ANDREW-Li-33/john-stockbot-3651/CAD files/flywheel printed parts/motor side inner bracket.stl

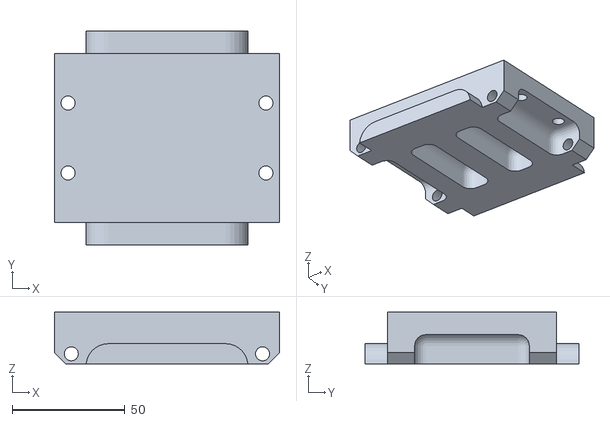
[picture p35: CAD file, 2026-05-08]
CAD files/flywheel printed parts/motor side inner bracket.stl
100.0 x 95.0 x 23.0
