ANDREW-Li-33/john-stockbot-3651/CAD files/drivetrain printed parts/wheel_90T_pulley.stl

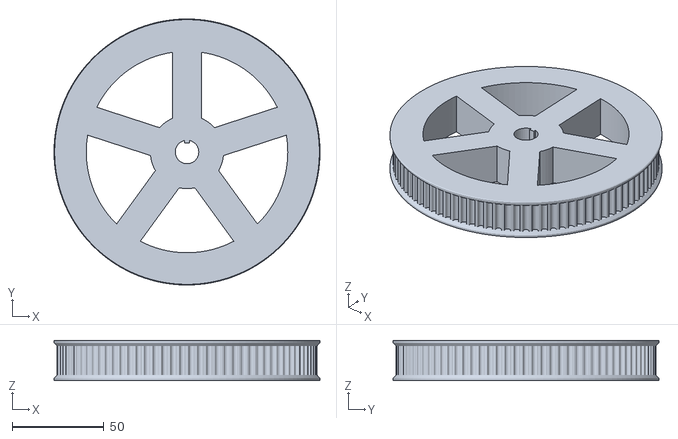
[picture p36: CAD file, 2026-05-08]
CAD files/drivetrain printed parts/wheel_90T_pulley.stl
145.2 x 145.2 x 22.0
