ANDREW-Li-33/john-stockbot-3651/CAD files/final project 3651/lighter_converyor_wheel.stl

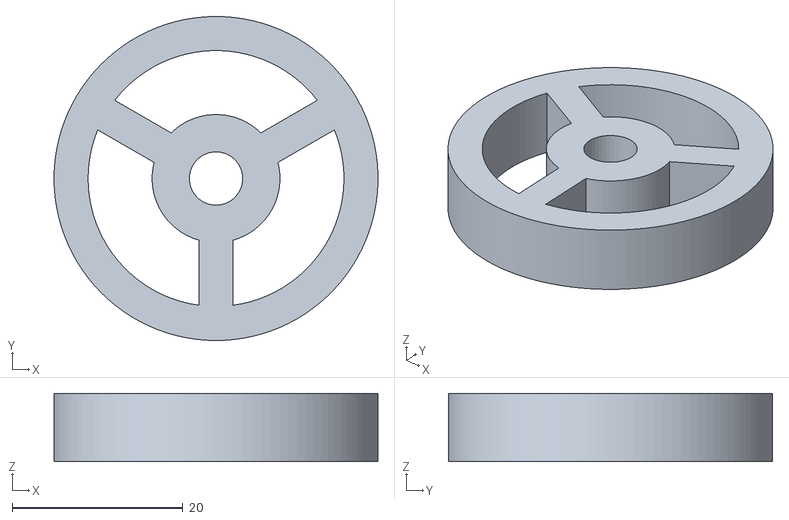
[picture p37: CAD file, 2026-05-08]
CAD files/final project 3651/lighter_converyor_wheel.stl
38.0 x 38.0 x 8.00
