ANDREW-Li-33/john-stockbot-3651/CAD files/drivetrain printed parts/4mm_high_spacer.stl

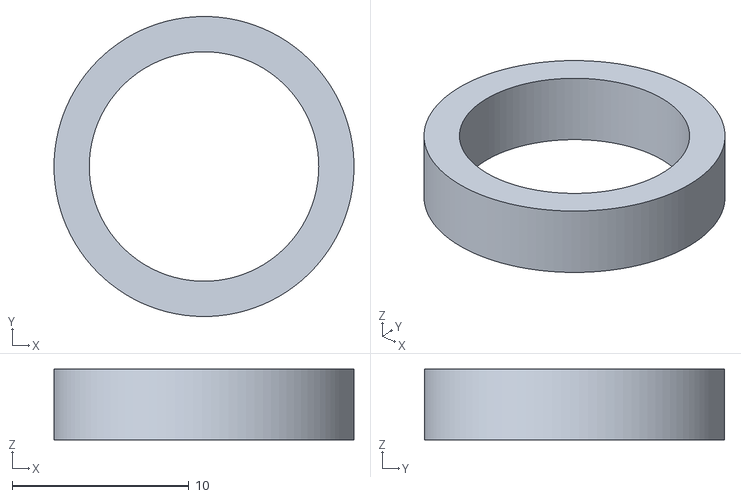
[picture p38: CAD file, 2026-05-08]
CAD files/drivetrain printed parts/4mm_high_spacer.stl
17.0 x 17.0 x 4.00
