ANDREW-Li-33/john-stockbot-3651/CAD files/final project 3651/fuse_box_mount.stl

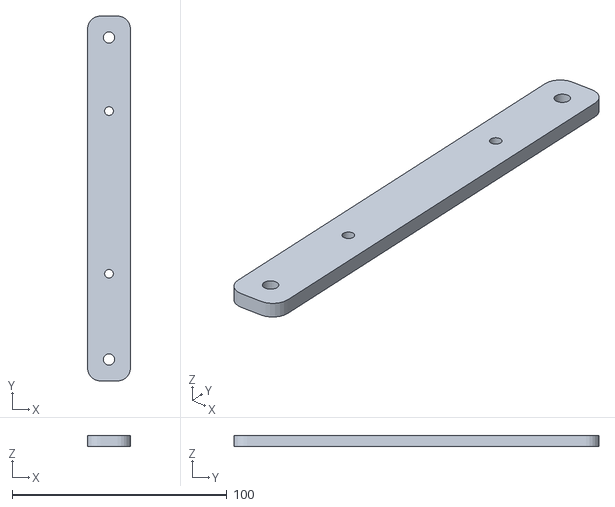
[picture p39: CAD file, 2026-05-08]
CAD files/final project 3651/fuse_box_mount.stl
20.0 x 169.8 x 5.00
