ANDREW-Li-33/john-stockbot-3651/CAD files/drivetrain printed parts/large_non_motor_side_connector.stl

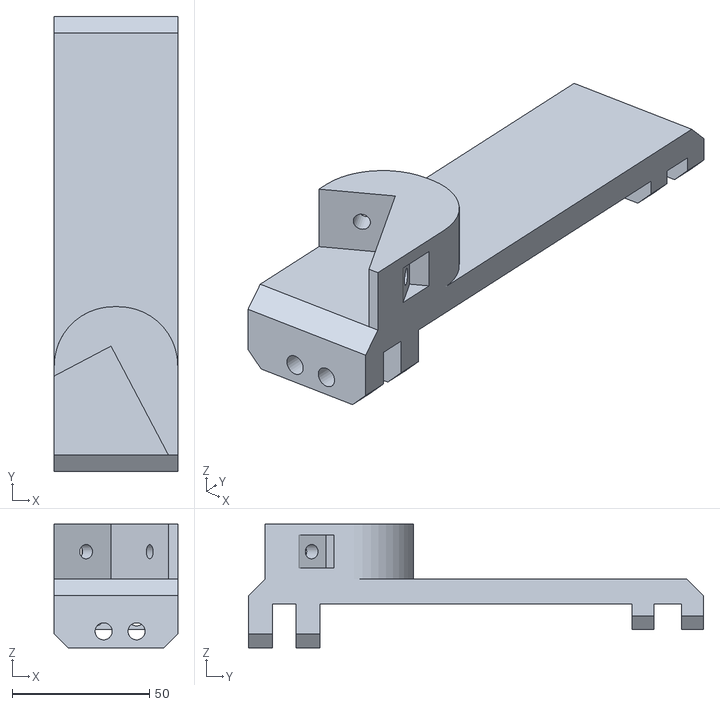
[picture p40: CAD file, 2026-05-08]
CAD files/drivetrain printed parts/large_non_motor_side_connector.stl
45.0 x 165.7 x 45.0
