ANDREW-Li-33/john-stockbot-3651/CAD files/final project 3651/wheel_conveyor_holder.stl

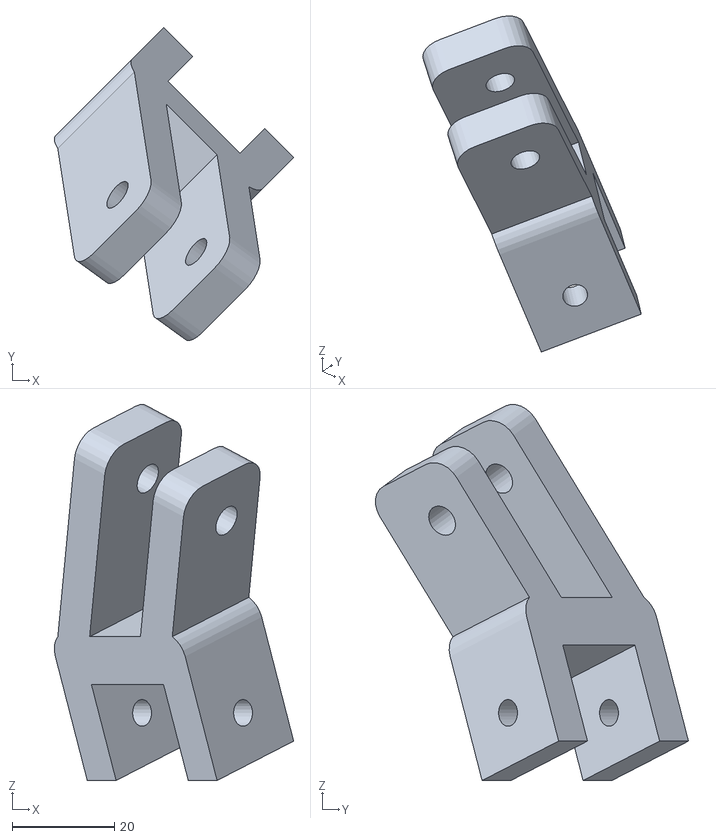
[picture p41: CAD file, 2026-05-08]
CAD files/final project 3651/wheel_conveyor_holder.stl
46.9 x 61.4 x 73.7
