ANDREW-Li-33/john-stockbot-3651/CAD files/drivetrain printed parts/intermediate_20T_pulley.stl

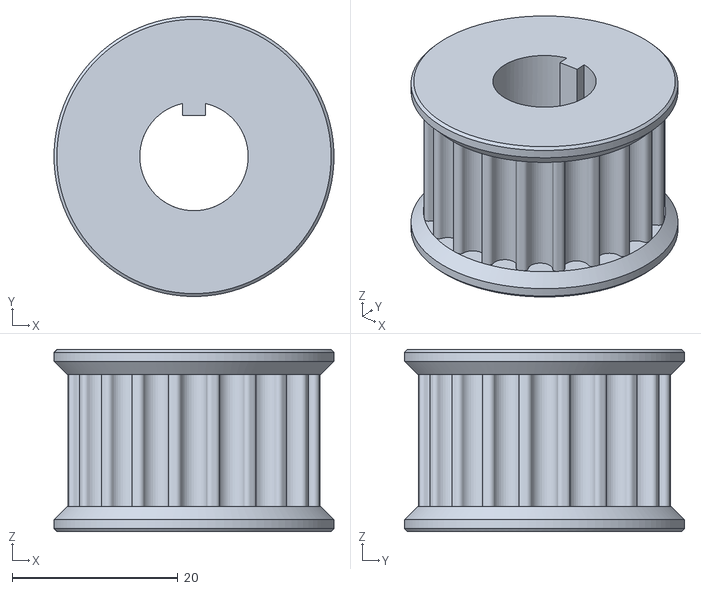
[picture p42: CAD file, 2026-05-08]
CAD files/drivetrain printed parts/intermediate_20T_pulley.stl
33.8 x 33.8 x 22.0
