ANDREW-Li-33/john-stockbot-3651/CAD files/final project 3651/servo_mount.stl

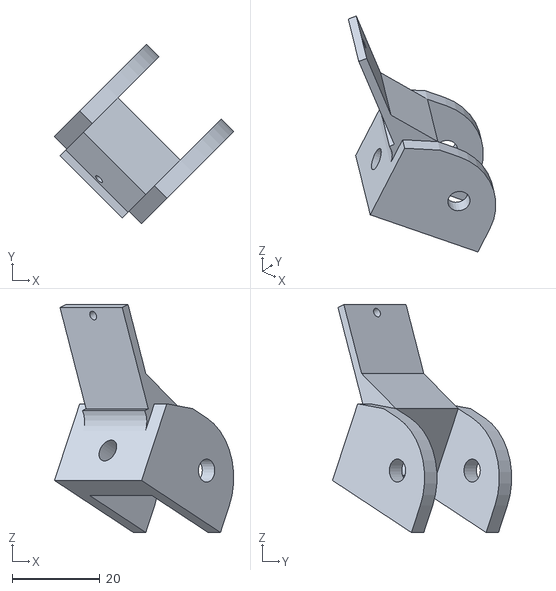
[picture p43: CAD file, 2026-05-08]
CAD files/final project 3651/servo_mount.stl
40.7 x 40.7 x 51.8
