ANDREW-Li-33/john-stockbot-3651/CAD files/final project 3651/testing_plate_dual_esc.stl

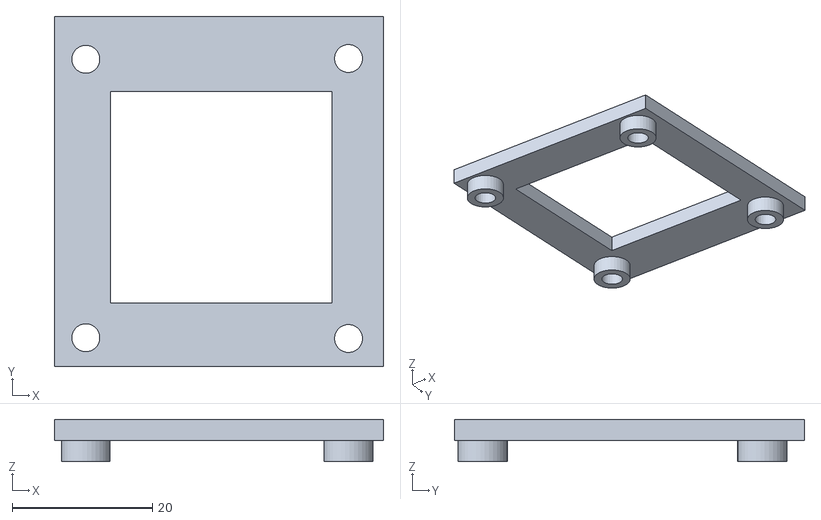
[picture p44: CAD file, 2026-05-08]
CAD files/final project 3651/testing_plate_dual_esc.stl
47.0 x 50.0 x 6.00
