ANDREW-Li-33/john-stockbot-3651/CAD files/final project 3651/bottom_conveyor_mount.stl

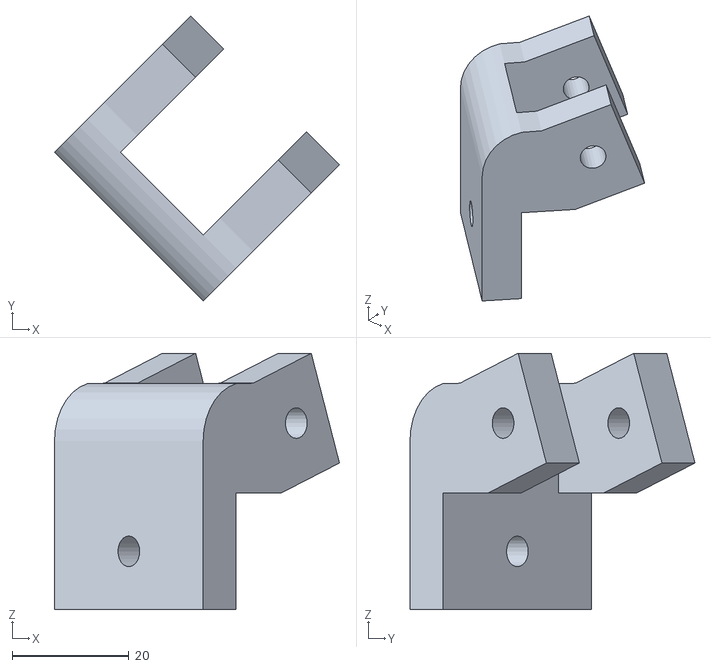
[picture p45: CAD file, 2026-05-08]
CAD files/final project 3651/bottom_conveyor_mount.stl
48.8 x 48.8 x 43.9
