ANDREW-Li-33/john-stockbot-3651/CAD files/final project 3651/conveyor_mount.stl

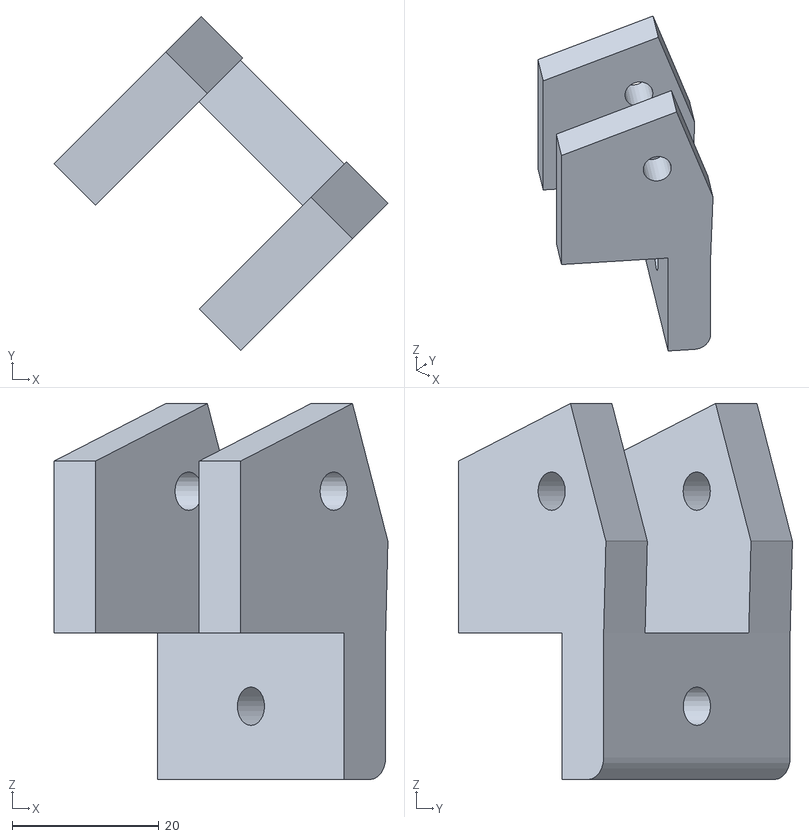
[picture p46: CAD file, 2026-05-08]
CAD files/final project 3651/conveyor_mount.stl
45.6 x 45.6 x 51.3
