ANDREW-Li-33/john-stockbot-3651/CAD files/final project 3651/gate_stick.stl

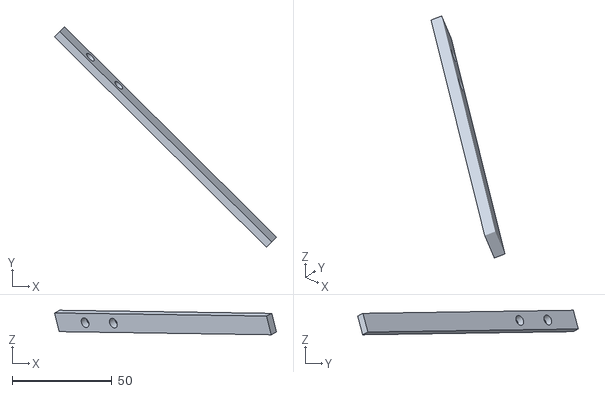
[picture p47: CAD file, 2026-05-08]
CAD files/final project 3651/gate_stick.stl
111.5 x 110.8 x 12.3
