ANDREW-Li-33/john-stockbot-3651/CAD files/final project 3651/conveyor_wheel.stl

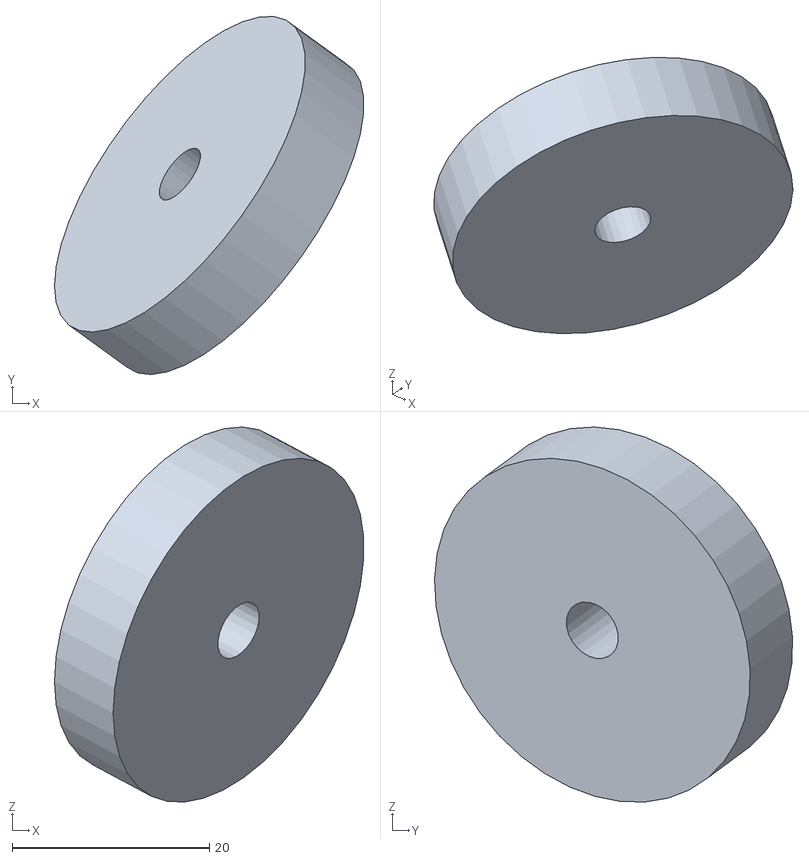
[picture p48: CAD file, 2026-05-08]
CAD files/final project 3651/conveyor_wheel.stl
31.3 x 36.3 x 38.0
