ANDREW-Li-33/john-stockbot-3651/CAD files/final project 3651/dual_drivetrain_esc_testing_plate.stl

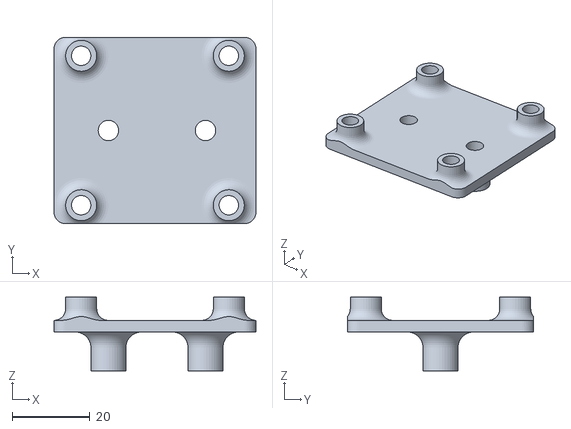
[picture p49: CAD file, 2026-05-08]
CAD files/final project 3651/dual_drivetrain_esc_testing_plate.stl
52.0 x 48.0 x 19.0
