ANDREW-Li-33/john-stockbot-3651/CAD files/final project 3651/battery_mount.stl

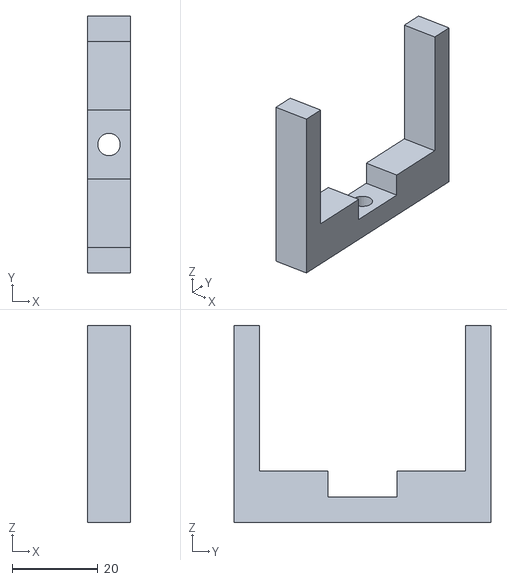
[picture p50: CAD file, 2026-05-08]
CAD files/final project 3651/battery_mount.stl
10.0 x 60.0 x 46.0
