ANDREW-Li-33/john-stockbot-3651/CAD files/final project 3651/bus_bar_holder.stl

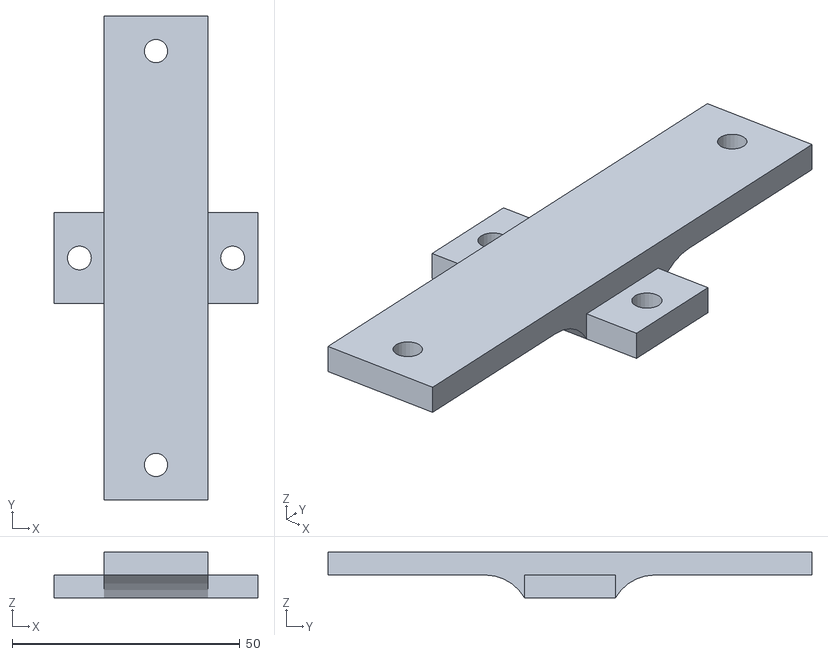
[picture p51: CAD file, 2026-05-08]
CAD files/final project 3651/bus_bar_holder.stl
44.7 x 106.3 x 10.0
