ANDREW-Li-33/john-stockbot-3651/CAD files/final project 3651/slide_mounting_m6_spacer.stl

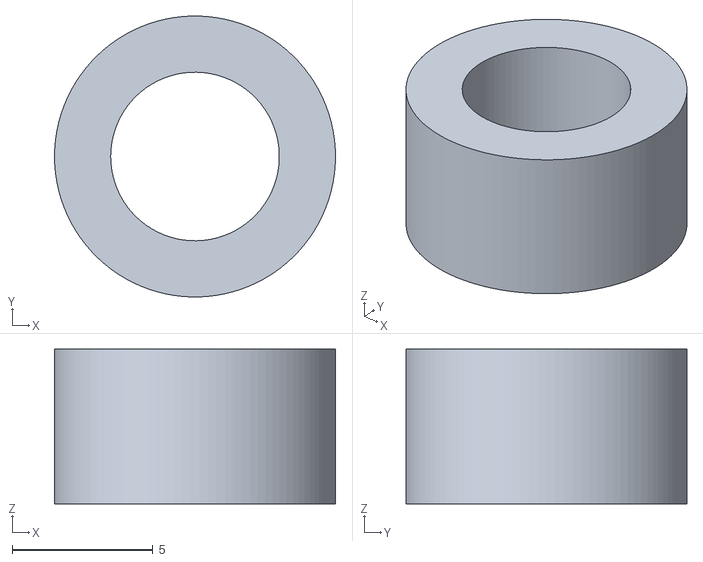
[picture p53: CAD file, 2026-05-08]
CAD files/final project 3651/slide_mounting_m6_spacer.stl
10.0 x 10.00 x 5.50
